pekkaroi/bldc-drive/firmware/src/pid.c

/*
 	bldc-drive Cheap and simple brushless DC motor driver designed for CNC applications using STM32 microcontroller.
	Copyright (C) 2015 Pekka Roivainen

	Pid loop is based on F103ServoDrive project of Mihai.
	http://www.cnczone.com/forums/open-source-controller-boards/283428-cnc.html

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
	You should have received a copy of the GNU General Public License
	along with this program; if not, write to the Free Software
	Foundation, Inc., 51 Franklin Street, Fifth Floor, Boston, MA  02110-1301, USA.
*/

#include <stm32f10x_gpio.h>
#include <stdlib.h>
#include "pid.h"
#include "pwm.h"
#include "hall.h"
#include "encoder.h"
#include "input.h"
#include "configuration.h"

int32_t position_error;
int32_t pid_requested_position;
int32_t pid_last_requested_position;
int32_t pid_last_requested_position_delta;
volatile int32_t pid_integrated_error;
int32_t pid_prev_position_error;
uint32_t max_error; //statistics

volatile uint16_t duty;

void initPid()
{

	pid_requested_position=encoder_count;
	pid_integrated_error = 0;
	pid_prev_position_error =0;

	//TIM3 used for pid loop timing.
	RCC_APB1PeriphClockCmd(RCC_APB1Periph_TIM3, ENABLE);
	TIM_TimeBaseInitTypeDef TIM_TimeBaseStructure;
	TIM_TimeBaseStructure.TIM_Prescaler = 72; //1MHz counter
	TIM_TimeBaseStructure.TIM_CounterMode = TIM_CounterMode_Up;
	TIM_TimeBaseStructure.TIM_Period = PID_TIM_PERIOD; //4kHz update interval
	TIM_TimeBaseStructure.TIM_ClockDivision = 0;
	TIM_TimeBaseStructure.TIM_RepetitionCounter = 0;
	TIM_TimeBaseInit(TIM3, &TIM_TimeBaseStructure);
	TIM_ITConfig(TIM3, TIM_IT_Update, ENABLE);
	TIM_Cmd(TIM3, ENABLE);

	NVIC_InitTypeDef NVIC_InitStructure;
	NVIC_InitStructure.NVIC_IRQChannel = TIM3_IRQn;
	NVIC_InitStructure.NVIC_IRQChannelPreemptionPriority = 0x02;
	NVIC_InitStructure.NVIC_IRQChannelSubPriority = 1;
	NVIC_InitStructure.NVIC_IRQChannelCmd = ENABLE;
	NVIC_Init(&NVIC_InitStructure);

}
//This is called from TIM3 update interrupt. defined in input.c
void updatePid()
{

	uint32_t abs_position_error;
	int32_t position_delta;
	int32_t position_delta_delta;
	//getEncoderCount(); //this is dangerous to call from interrupt
	if (!motor_running)
	{
		pid_integrated_error=0;
		return;



	}



	position_error = encoder_count - pid_requested_position;

	position_delta= pid_requested_position - pid_last_requested_position;
	position_delta_delta = position_delta - pid_last_requested_position_delta;

	pid_last_requested_position = pid_requested_position;
	pid_last_requested_position_delta = position_delta;

	abs_position_error = abs(position_error);
	if(abs_position_error < s.pid_deadband)
	{
		position_error=0;
	}
	else if (position_error > 0)
		position_error -= s.pid_deadband;
	else
		position_error += s.pid_deadband;

	if(abs_position_error > max_error)
			max_error = abs_position_error;



	if (abs_position_error > s.max_error)
	{
	      pwm_motorStop();
	      ERROR_LED_ON;
	      return;

	}
//P
	int32_t output = position_error * s.pid_Kp;

//I
	pid_integrated_error += position_error * s.pid_Ki;
	if (pid_integrated_error > 400000)
		pid_integrated_error = 400000;
	if (pid_integrated_error < -400000)
		pid_integrated_error = -400000;

	output += pid_integrated_error;
//D
	output += (position_error - pid_prev_position_error) * s.pid_Kd;
	pid_prev_position_error = position_error;


//FF1
	output += position_delta * s.pid_FF1;
//FF2
	output += position_delta_delta * s.pid_FF2;

	output /= 100; //provide larger dynamic range for pid. (without this, having pid_Ki = 1 was enough for oscillation.

    //limit output power
	if (output > MAX_DUTY)
		output = MAX_DUTY;
	if (output < -MAX_DUTY)
		output = -MAX_DUTY;
	if(output>0)
	{
		dir=0;

	}
	else
	{
		dir=1;

	}
	duty = abs(output);

	pwm_setDutyCycle();



}
