pekkaroi/bldc-drive/firmware/src/adc.c

/*
 	bldc-drive Cheap and simple brushless DC motor driver designed for CNC applications using STM32 microcontroller.
	Copyright (C) 2015 Pekka Roivainen

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
	You should have received a copy of the GNU General Public License
	along with this program; if not, write to the Free Software
	Foundation, Inc., 51 Franklin Street, Fifth Floor, Boston, MA  02110-1301, USA.
*/

#include <stm32f10x_adc.h>
#include <stm32f10x_dma.h>
#include <stm32f10x_gpio.h>
#include <stm32f10x_tim.h>
#include <stm32f10x_rcc.h>
//#include <>

#include "adc.h"
#include "pwm.h"


volatile uint16_t ADC_value;
volatile uint16_t max_duty;

void initADC()
{

	max_duty=MAX_DUTY;
	GPIO_InitTypeDef GPIO_InitStructure;
	//--Enable ADC1 and GPIOA--
	RCC_APB2PeriphClockCmd(RCC_APB2Periph_ADC1 | RCC_APB2Periph_GPIOA, ENABLE);


	GPIO_StructInit(&GPIO_InitStructure);
	GPIO_InitStructure.GPIO_Pin = GPIO_Pin_4; //PA4 = bus measurement
	GPIO_InitStructure.GPIO_Mode = GPIO_Mode_AIN;
	GPIO_Init(GPIOA, &GPIO_InitStructure);

	ADC_InitTypeDef ADC_InitStructure;
	//ADC1 configuration

	ADC_InitStructure.ADC_Mode = ADC_Mode_Independent;
	ADC_InitStructure.ADC_ScanConvMode = DISABLE;

	ADC_InitStructure.ADC_ContinuousConvMode = DISABLE;//!

	ADC_InitStructure.ADC_ExternalTrigConv = ADC_ExternalTrigConv_None;

	ADC_InitStructure.ADC_DataAlign = ADC_DataAlign_Right;
	ADC_InitStructure.ADC_NbrOfChannel = 1;
	//load structure values to control and status registers
	ADC_Init(ADC1, &ADC_InitStructure);
	ADC_RegularChannelConfig(ADC1, ADC_Channel_4, 1, ADC_SampleTime_41Cycles5);
	//Enable ADC1
	ADC_Cmd(ADC1, ENABLE);
	//enable DMA for ADC
	ADC_DMACmd(ADC1, ENABLE);
	//Enable ADC1 reset calibration register
	ADC_ResetCalibration(ADC1);
	//Check the end of ADC1 reset calibration register
	while(ADC_GetResetCalibrationStatus(ADC1));
	//Start ADC1 calibration
	ADC_StartCalibration(ADC1);
	//Check the end of ADC1 calibration
	while(ADC_GetCalibrationStatus(ADC1));


	//enable DMA1 clock
	RCC_AHBPeriphClockCmd(RCC_AHBPeriph_DMA1, ENABLE);
	//create DMA structure
	DMA_InitTypeDef  DMA_InitStructure;
	//reset DMA1 channe1 to default values;
	DMA_DeInit(DMA1_Channel1);

	DMA_InitStructure.DMA_M2M = DMA_M2M_Disable;

	DMA_InitStructure.DMA_Mode = DMA_Mode_Circular;

	DMA_InitStructure.DMA_Priority = DMA_Priority_High;

	DMA_InitStructure.DMA_PeripheralDataSize = DMA_PeripheralDataSize_HalfWord;
	DMA_InitStructure.DMA_MemoryDataSize = DMA_MemoryDataSize_HalfWord;

	DMA_InitStructure.DMA_MemoryInc = DMA_MemoryInc_Disable;

	DMA_InitStructure.DMA_PeripheralInc = DMA_PeripheralInc_Disable;

	DMA_InitStructure.DMA_DIR = DMA_DIR_PeripheralSRC;

	DMA_InitStructure.DMA_BufferSize = 1;

	DMA_InitStructure.DMA_PeripheralBaseAddr = (uint32_t)&ADC1->DR;
	DMA_InitStructure.DMA_MemoryBaseAddr = (uint32_t)&ADC_value;
	//send values to DMA registers
	DMA_Init(DMA1_Channel1, &DMA_InitStructure);
	// Enable DMA1 Channel Transfer Complete interrupt
	DMA_ITConfig(DMA1_Channel1, DMA_IT_TC, ENABLE);
	DMA_Cmd(DMA1_Channel1, ENABLE); //Enable the DMA1 - Channel1

	//Enable DMA1 channel IRQ Channel */
	NVIC_InitTypeDef NVIC_InitStructure;
	NVIC_InitStructure.NVIC_IRQChannel = DMA1_Channel1_IRQn;
	NVIC_InitStructure.NVIC_IRQChannelPreemptionPriority = 0;
	NVIC_InitStructure.NVIC_IRQChannelSubPriority = 0;
	NVIC_InitStructure.NVIC_IRQChannelCmd = ENABLE;
	NVIC_Init(&NVIC_InitStructure);

}

void ADC1_2_IRQHandler(void) {
  if (ADC_GetITStatus(ADC1, ADC_IT_EOC) != RESET)
  {

	  ADC_ClearITPendingBit(ADC1, ADC_IT_EOC);

  }
}


void DMA1_Channel1_IRQHandler(void) {
  if(DMA_GetITStatus(DMA1_IT_TC1)) {
	DMA_ClearITPendingBit(DMA1_IT_GL1);
	DMA_Cmd(DMA1_Channel1, ENABLE);
	if(ADC_value>s.max_current && max_duty>1)
	{
		max_duty -= 2;
		return;
	}
	if(ADC_value<=s.max_current && max_duty<MAX_DUTY)
	{
		max_duty ++;
		return;
	}




  }
}
